ak66666/ThumbsUp-Trackball-v4/Dongle Case/Cura Positioning.png

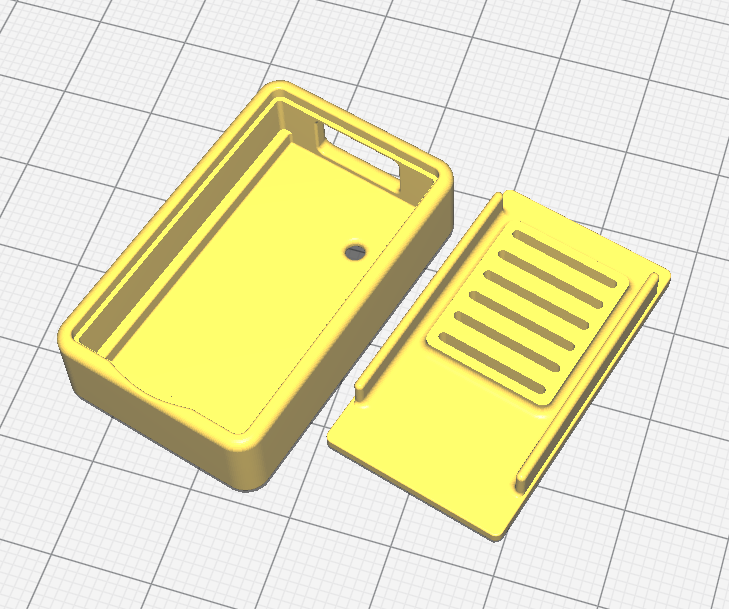
Dongle Case/Cura Positioning.png
