ak66666/ThumbsUp-Trackball-v4/Dongle Case/Dongle without Lid.jpg

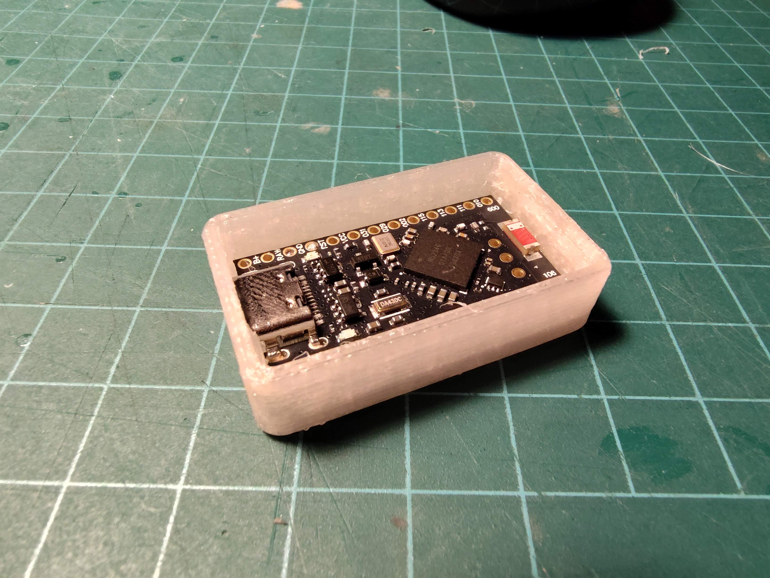
Dongle Case/Dongle without Lid.jpg
