ak66666/ThumbsUp-Trackball-v4/Dongle Case/Model.png

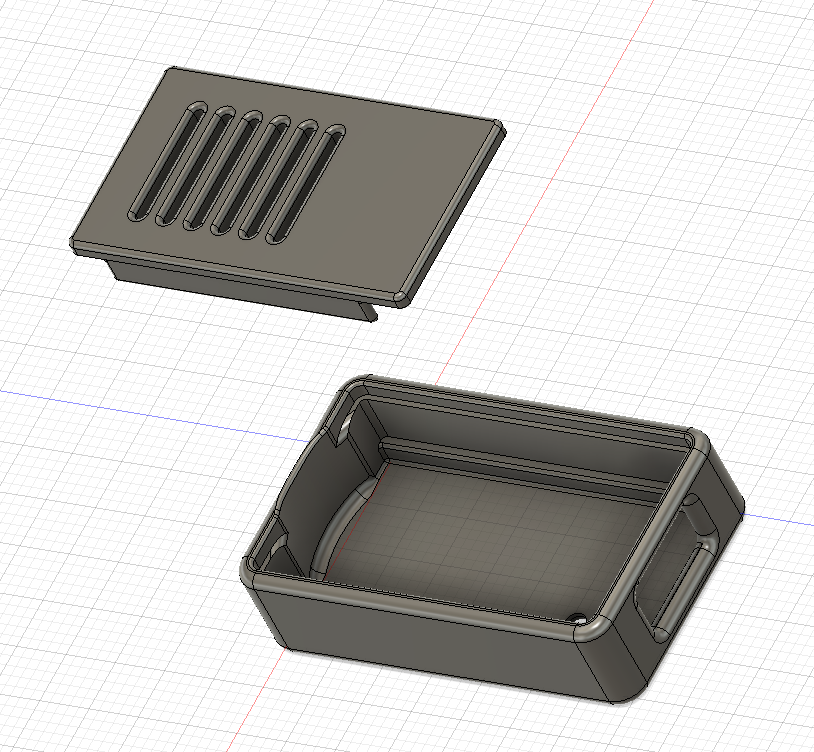
Dongle Case/Model.png
