ak66666/ThumbsUp-Trackball-v4/Kicad/Trackball/Pictures/PCBs.jpg

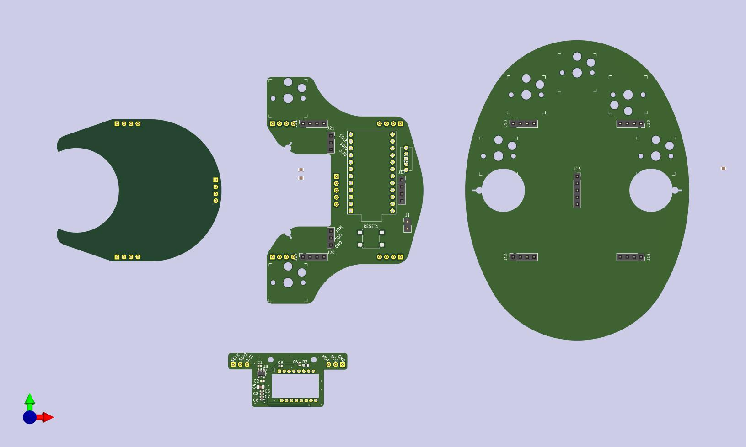
Kicad/Trackball/Pictures/PCBs.jpg
