ak66666/ThumbsUp-Trackball-v4/Photos/B4_rev2/123504665_HDR.jpg

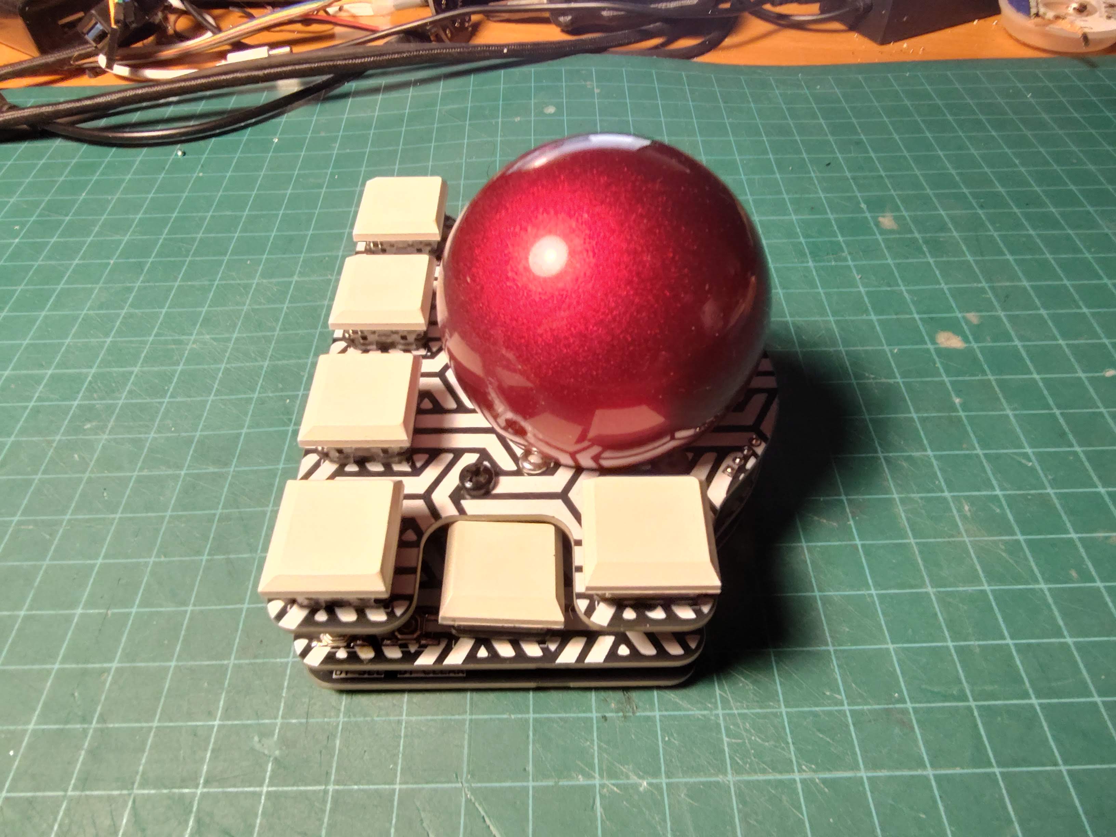
Photos/B4_rev2/123504665_HDR.jpg
