ak66666/ThumbsUp-Trackball-v4/Photos/B4_rev2/123514618_HDR.jpg

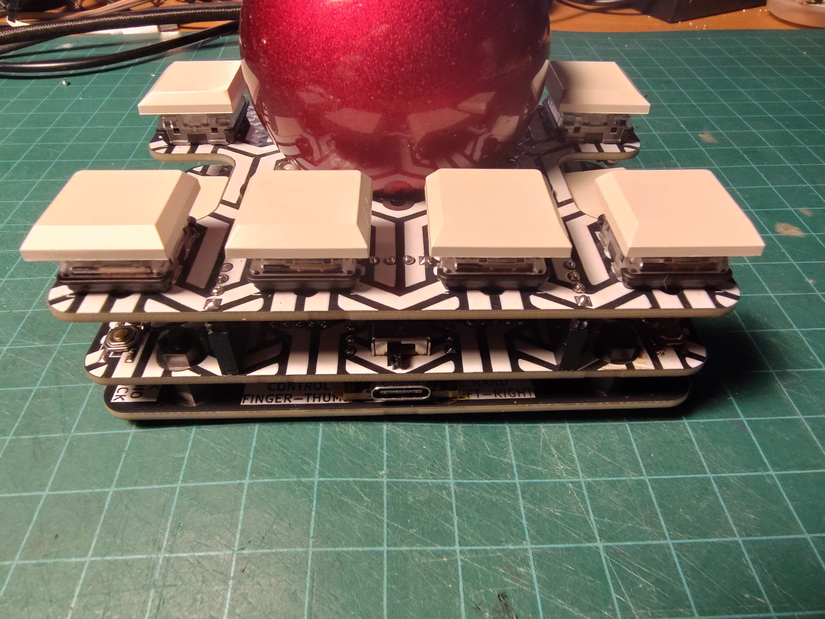
Photos/B4_rev2/123514618_HDR.jpg
