ak66666/ThumbsUp-Trackball-v4/Dongle Case/Dongle Parts.jpg

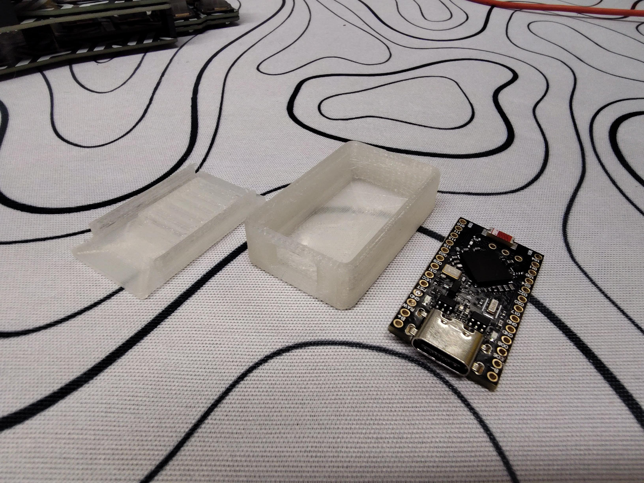
Dongle Case/Dongle Parts.jpg
